abl20/Autonomous-Robot-with-multiple-functions-based-on-Arduino./Photos/20171107_162431.jpg

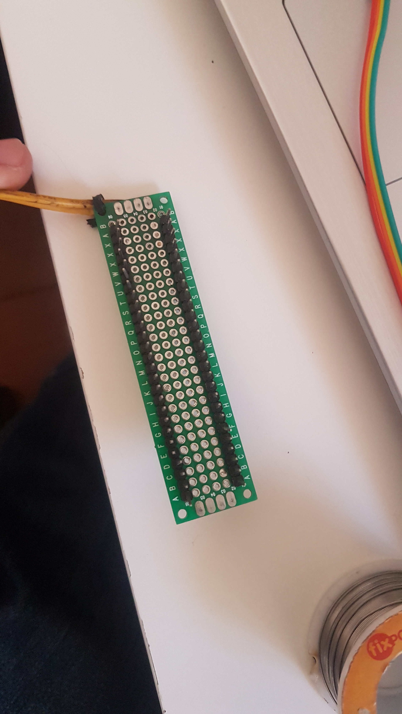
Photos/20171107_162431.jpg
