abl20/Autonomous-Robot-with-multiple-functions-based-on-Arduino./Photos/20171107_162447.jpg

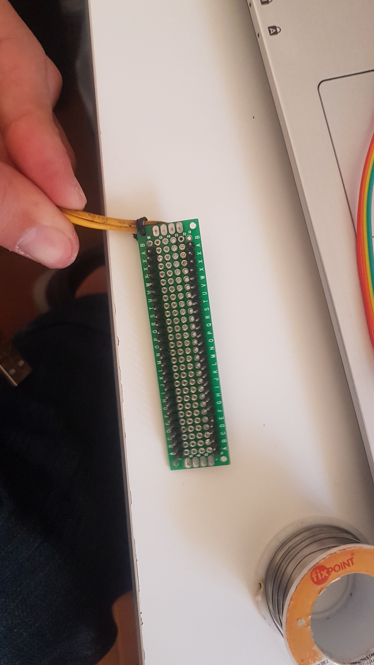
Photos/20171107_162447.jpg
