abl20/Autonomous-Robot-with-multiple-functions-based-on-Arduino./Photos/20171217_175608.jpg

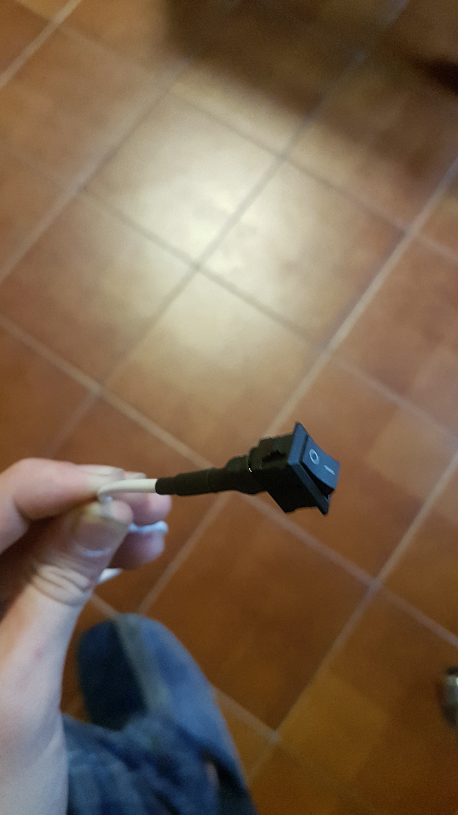
Photos/20171217_175608.jpg
