abl20/Autonomous-Robot-with-multiple-functions-based-on-Arduino./Photos/20180110_174055.jpg

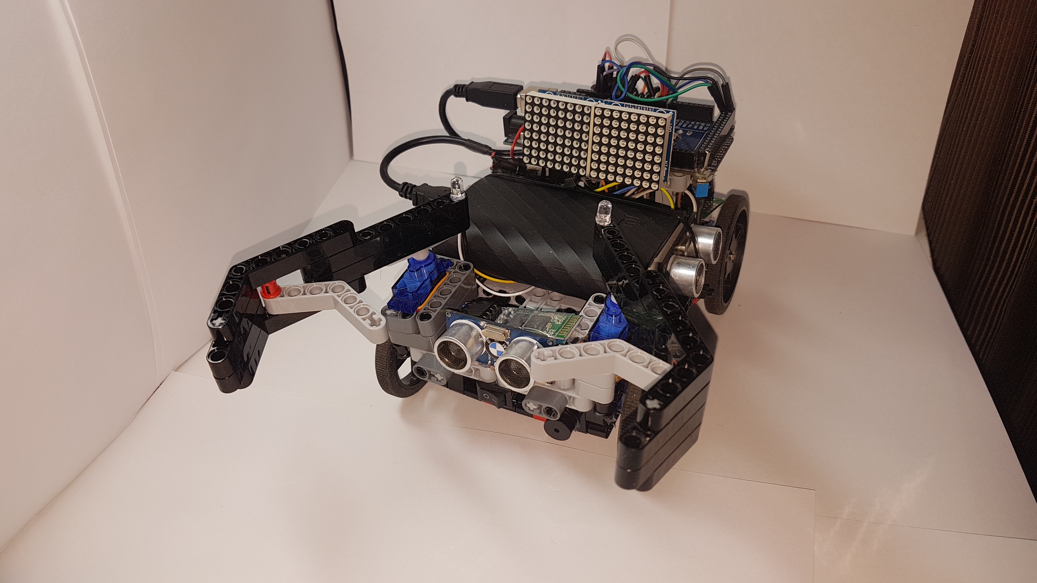
Photos/20180110_174055.jpg
