abl20/Autonomous-Robot-with-multiple-functions-based-on-Arduino./Photos/cables3.jpeg

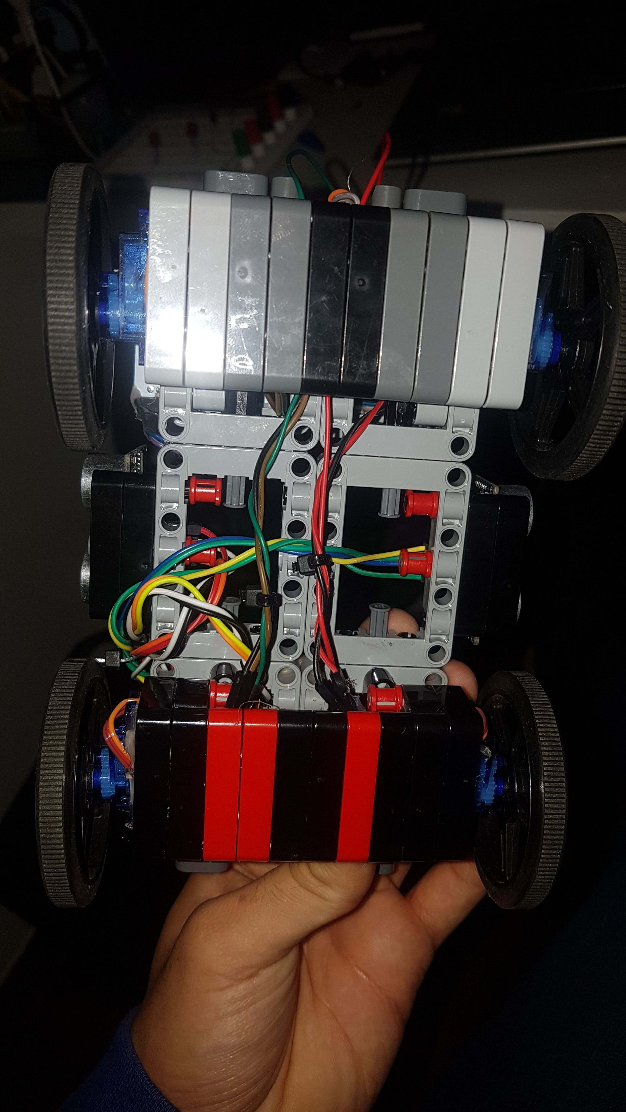
Photos/cables3.jpeg
