abl20/Autonomous-Robot-with-multiple-functions-based-on-Arduino./Photos/estructura2.jpeg

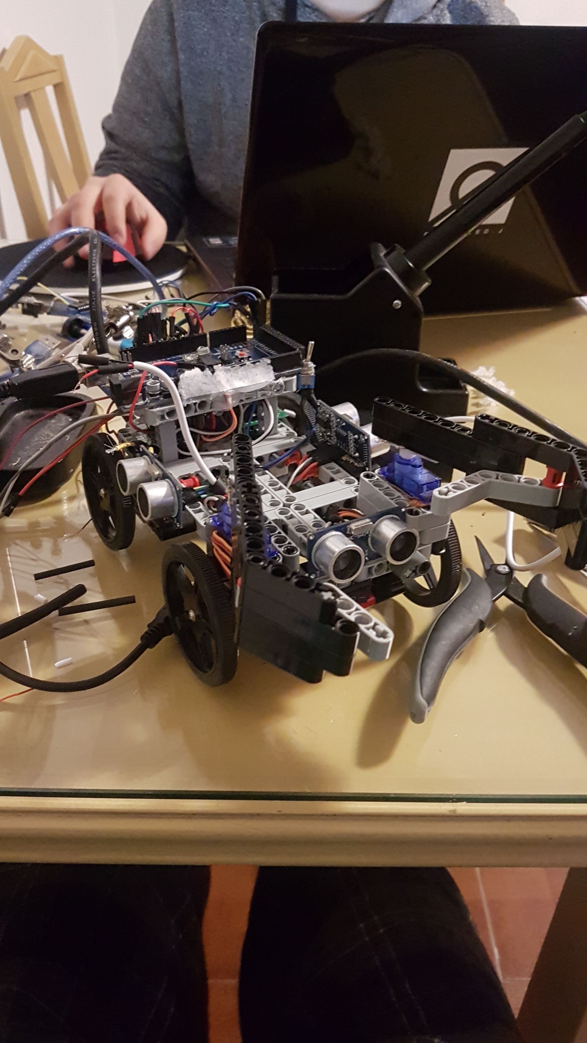
Photos/estructura2.jpeg
