abl20/Autonomous-Robot-with-multiple-functions-based-on-Arduino./Photos/estructura3.jpeg

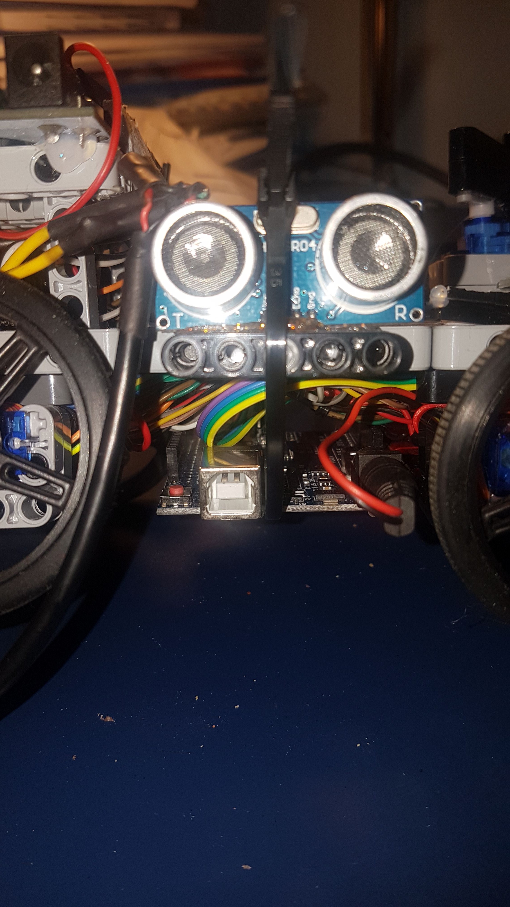
Photos/estructura3.jpeg
