abl20/Autonomous-Robot-with-multiple-functions-based-on-Arduino./Photos/estructura 1.jpeg

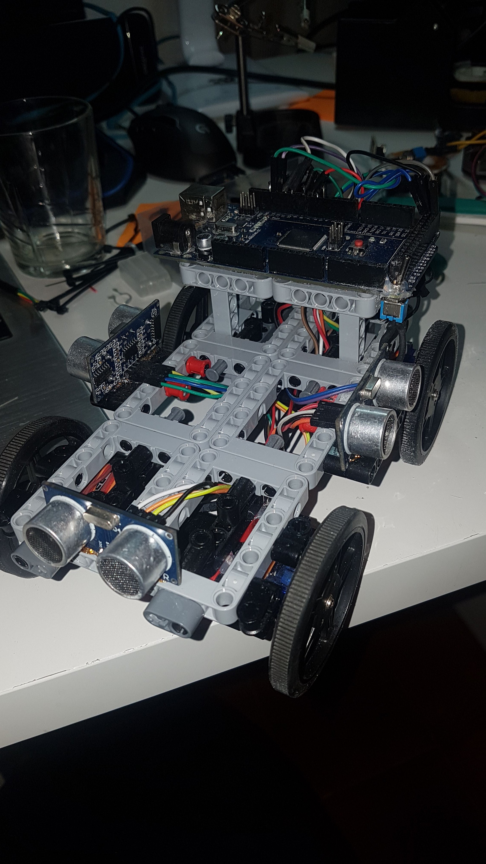
Photos/estructura 1.jpeg
