abl20/Autonomous-Robot-with-multiple-functions-based-on-Arduino./Photos/IMG-20171107-WA0069.jpeg

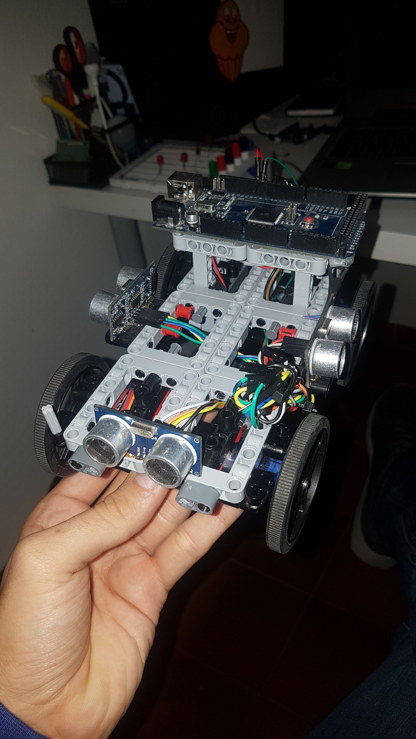
Photos/IMG-20171107-WA0069.jpeg
