abl20/Autonomous-Robot-with-multiple-functions-based-on-Arduino./Photos/IMG-20171112-WA0048.jpeg

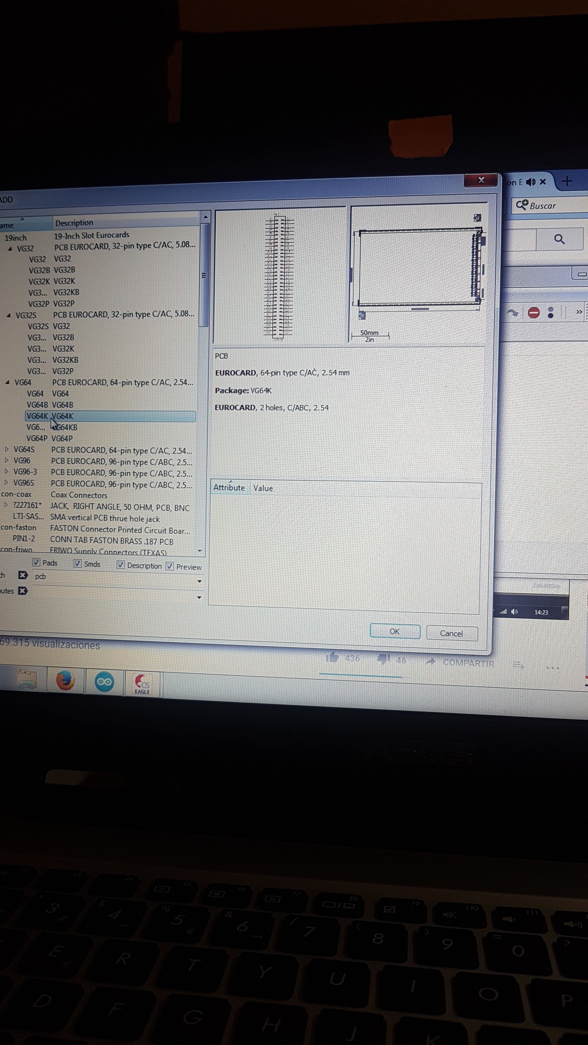
Photos/IMG-20171112-WA0048.jpeg
