abl20/Autonomous-Robot-with-multiple-functions-based-on-Arduino./Photos/IMG-20171112-WA0055.jpeg

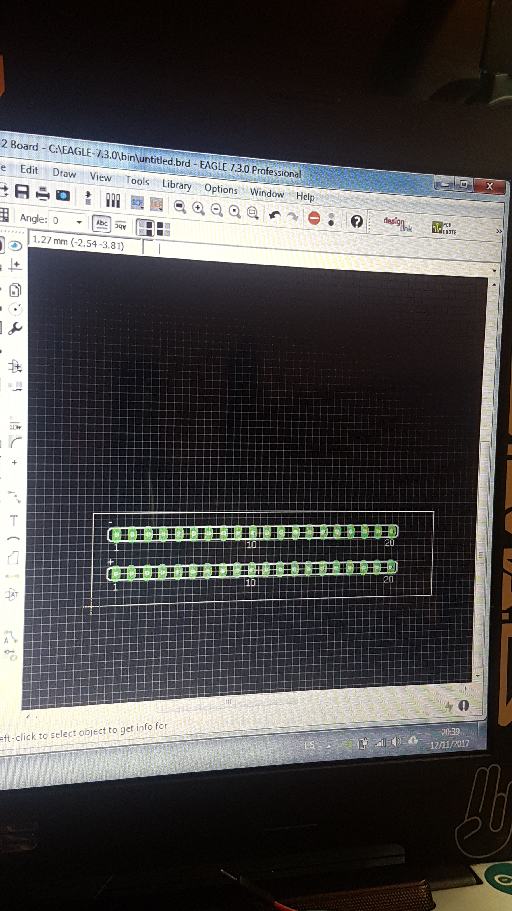
Photos/IMG-20171112-WA0055.jpeg
