abl20/Autonomous-Robot-with-multiple-functions-based-on-Arduino./Photos/IMG-20171217-WA0062.jpeg

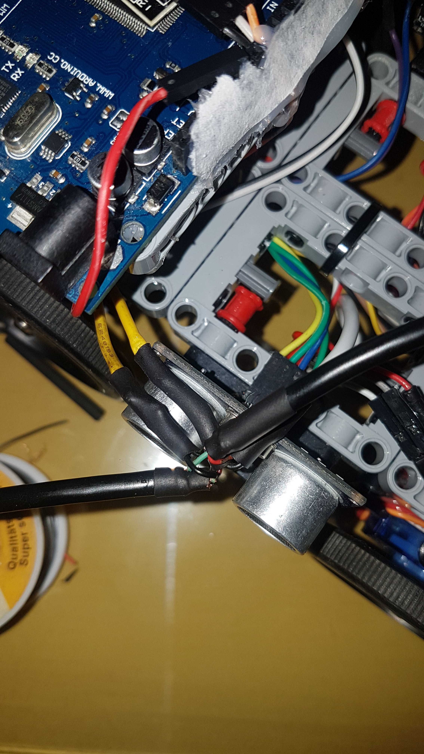
Photos/IMG-20171217-WA0062.jpeg
