abl20/Autonomous-Robot-with-multiple-functions-based-on-Arduino./Photos/IMG-20171226-WA0026.jpeg

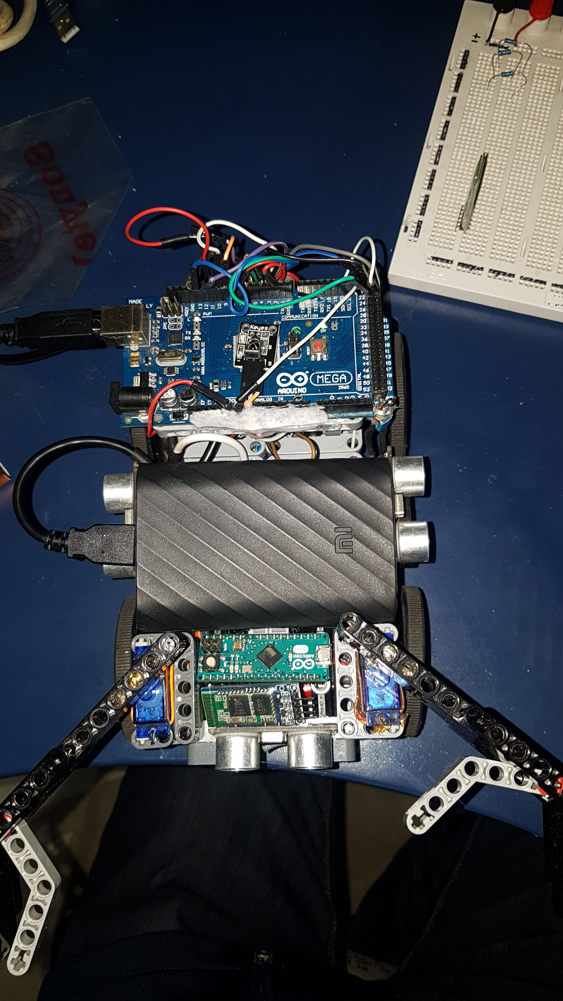
Photos/IMG-20171226-WA0026.jpeg
