abl20/Autonomous-Robot-with-multiple-functions-based-on-Arduino./Photos/IMG-20171230-WA0006.jpeg

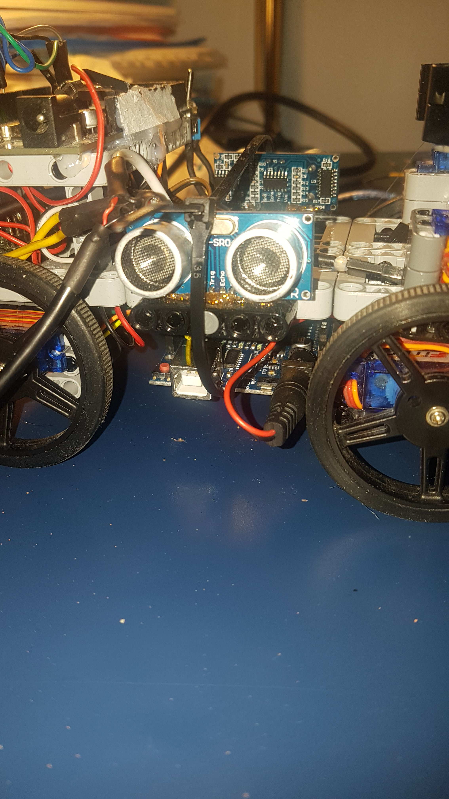
Photos/IMG-20171230-WA0006.jpeg
