abl20/Autonomous-Robot-with-multiple-functions-based-on-Arduino./Photos/IR LIB.jpg

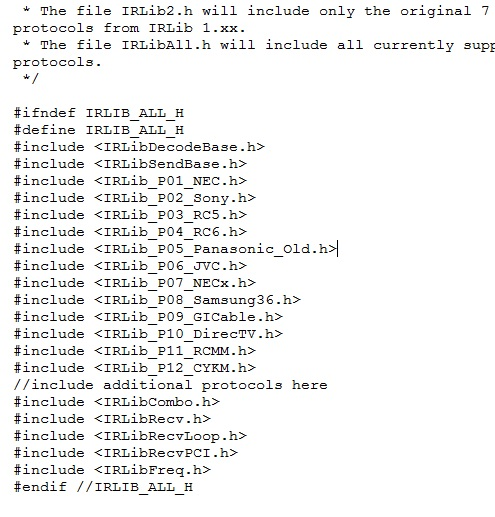
Photos/IR LIB.jpg
