abl20/Autonomous-Robot-with-multiple-functions-based-on-Arduino./PCB Design File in Eagle/PCB ALIMENTACION.sch

## EAGLE design PCB Design File in Eagle/PCB ALIMENTACION.sch (2018-12-06)

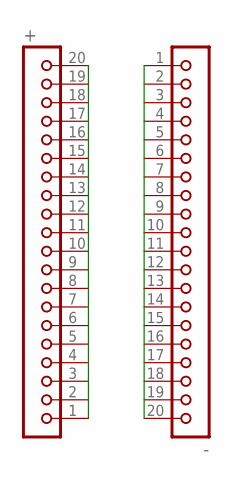
[picture p54: schematic PCB ALIMENTACION.sch]

Parts:
+: JBK20
-: JBK20

Connections:
unnamed: +.1, +.20
unnamed: -.1, -.20
